Aryan-G4/HeartSynch---IoT-Biometric-Sensor/Mechanical/solidworks/Arm Clamp inner v3.1.SLDPRT

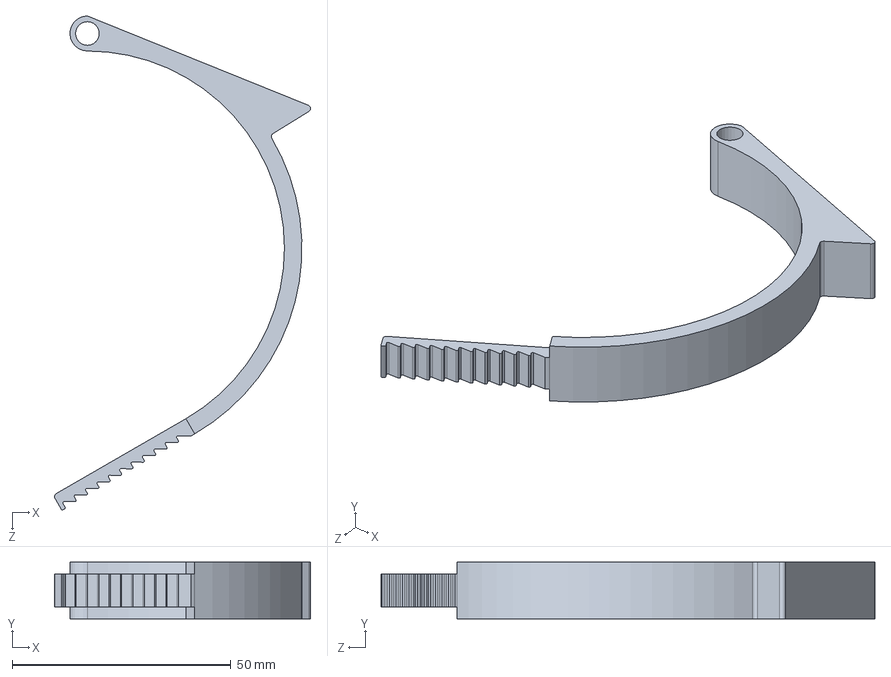
[picture p15: CAD file, 2024-01-21, an earlier design]
Mechanical/solidworks/Arm Clamp inner v3.1.SLDPRT
58.5 x 13.0 x 112.8 mm
