Aryan-G4/HeartSynch---IoT-Biometric-Sensor/Mechanical/solidworks/Arm Clamp v3.3.SLDPRT

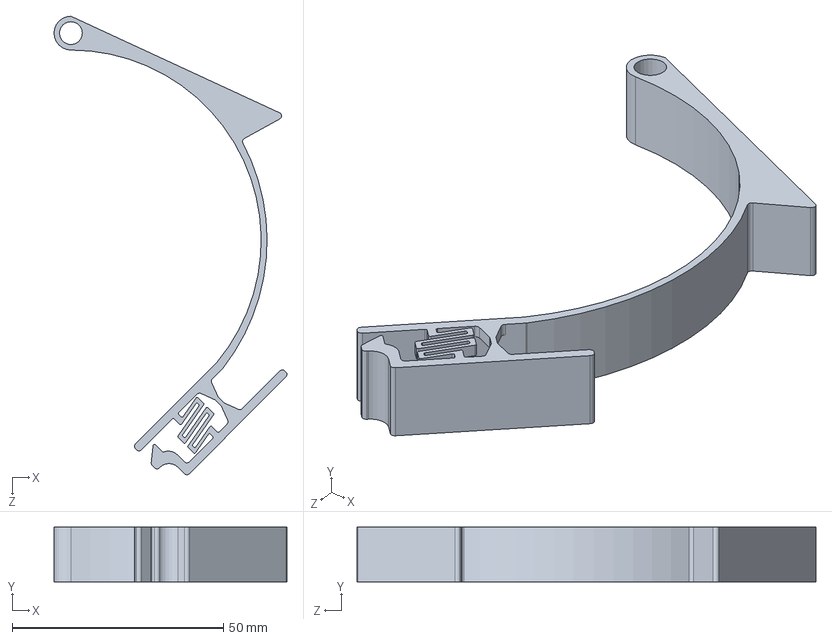
[picture p16: CAD file, 2024-01-21, an earlier design]
Mechanical/solidworks/Arm Clamp v3.3.SLDPRT
55.1 x 13.0 x 108.5 mm
