Aryan-G4/HeartSynch---IoT-Biometric-Sensor/Mechanical/solidworks/Arm Clamp v2.SLDPRT

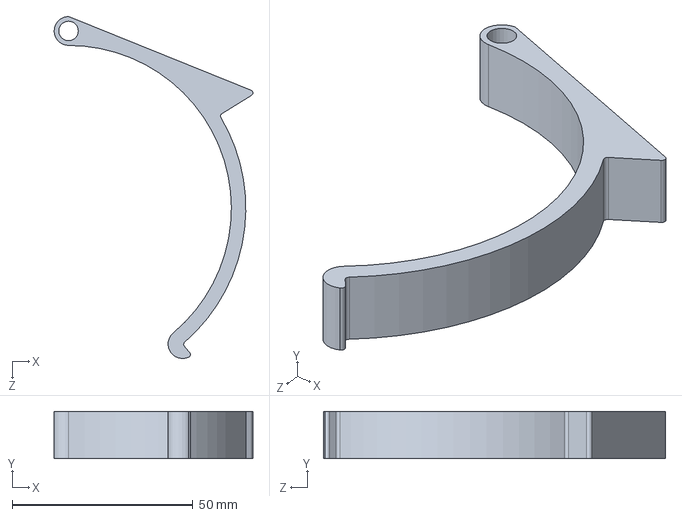
[picture p17: CAD file, 2024-01-21, an earlier design]
Mechanical/solidworks/Arm Clamp v2.SLDPRT
55.0 x 13.0 x 94.5 mm
